opinau/cv/Modul1/Docs/IMG_20200708_190415.jpg

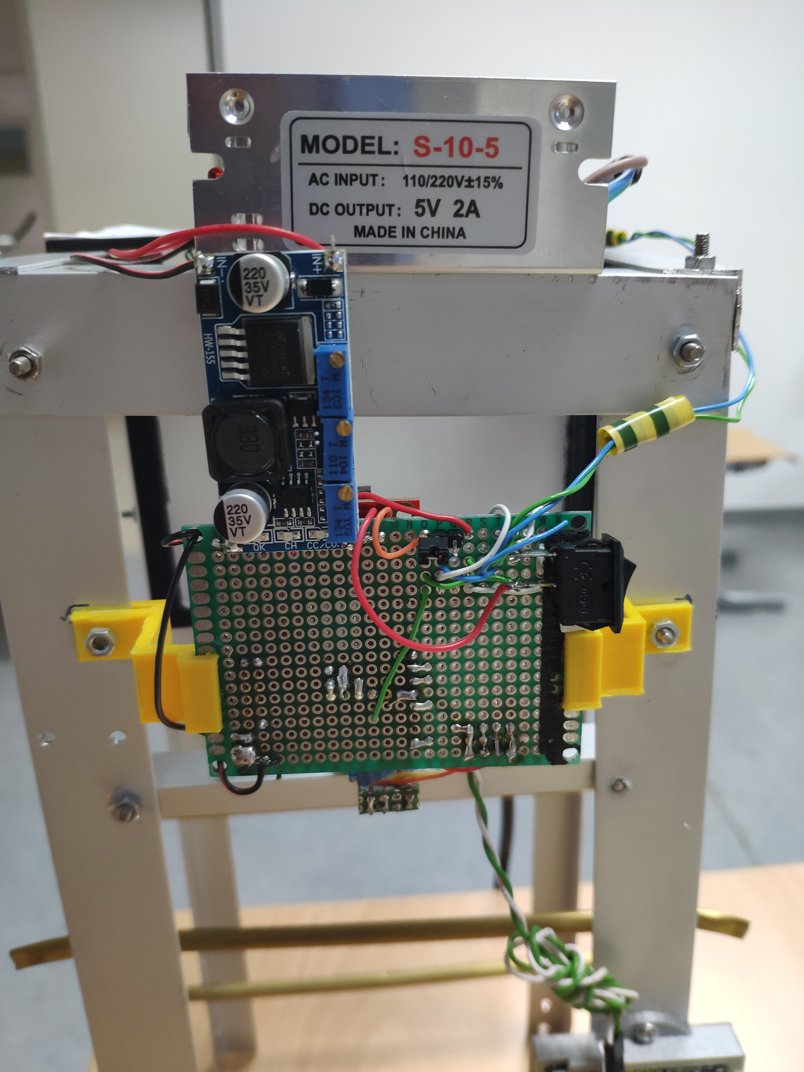
Modul1/Docs/IMG_20200708_190415.jpg
