opinau/cv/Modul1/Docs/IMG_20200708_190424.jpg

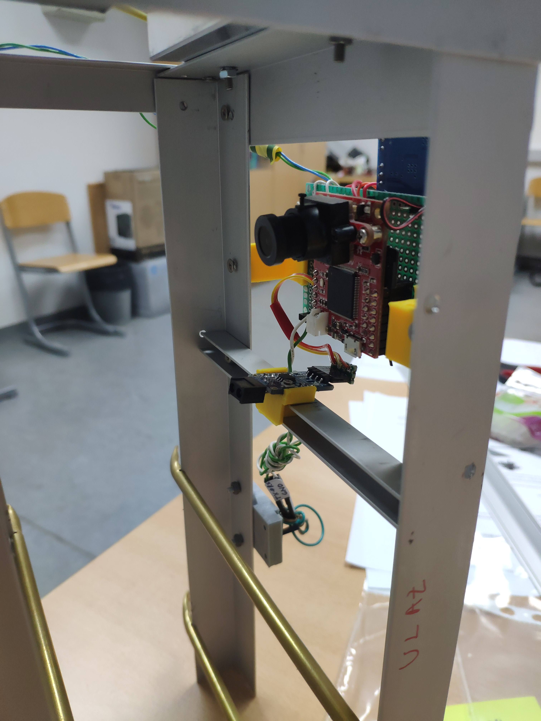
Modul1/Docs/IMG_20200708_190424.jpg
