opinau/cv/Modul1/Docs/visualisation_1.jpg

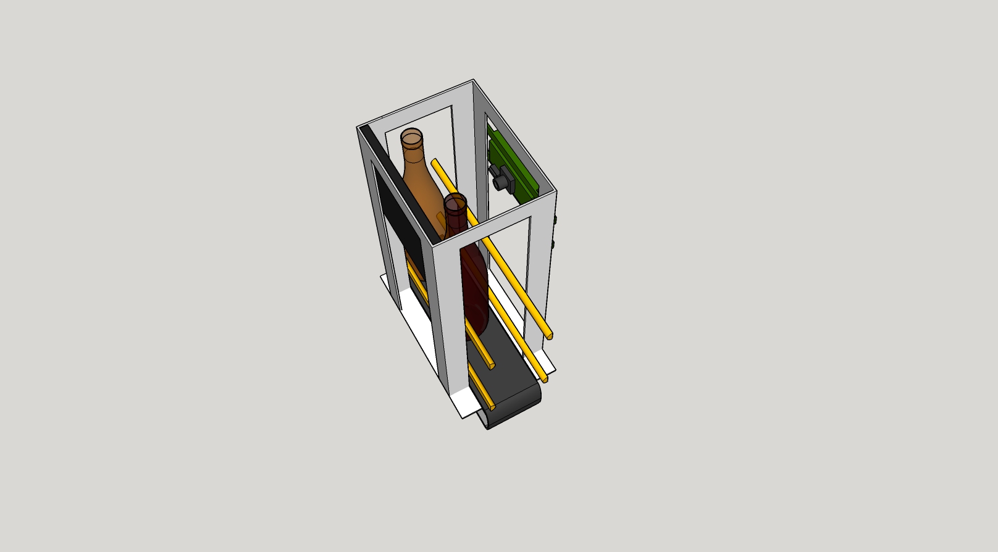
Modul1/Docs/visualisation_1.jpg
