opinau/cv/Modul1/Docs/visualisation_2.jpg

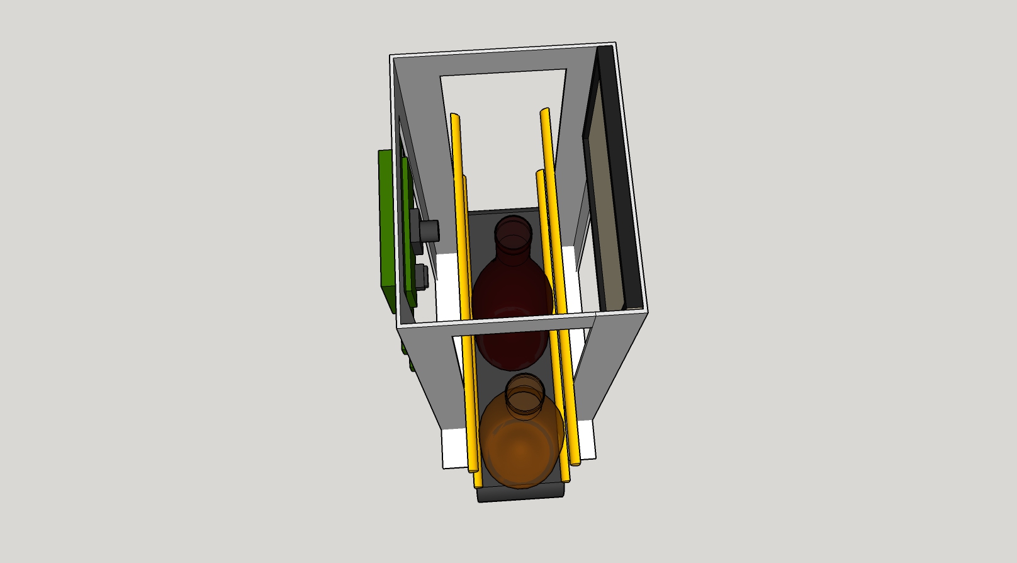
Modul1/Docs/visualisation_2.jpg
