opinau/cv/Modul1/Docs/visualisation_3.jpg

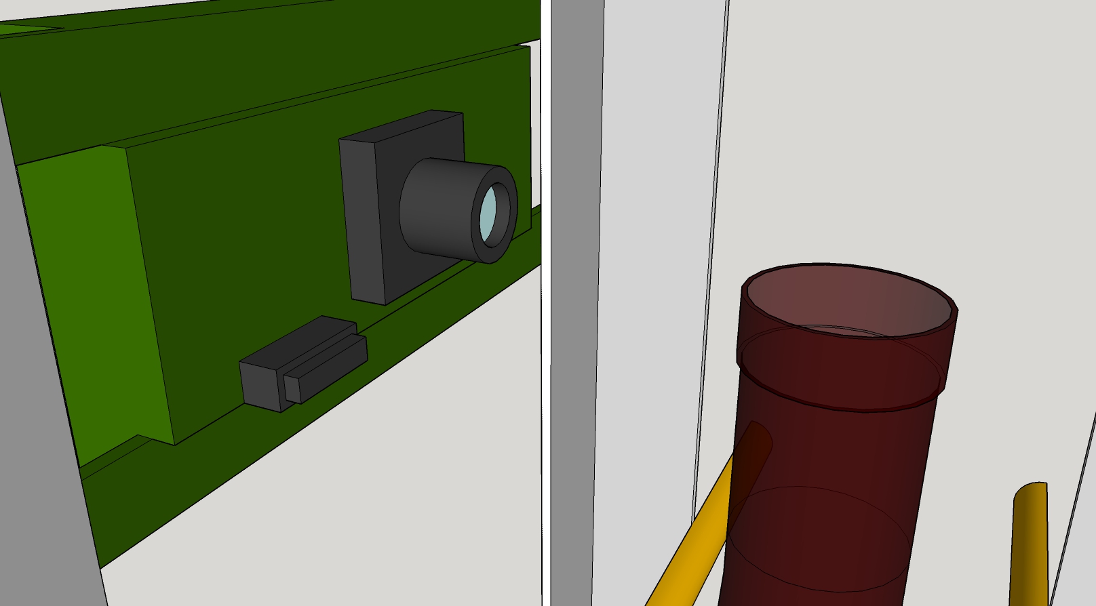
Modul1/Docs/visualisation_3.jpg
