opinau/cv/Modul1/Docs/visualisation_4.jpg

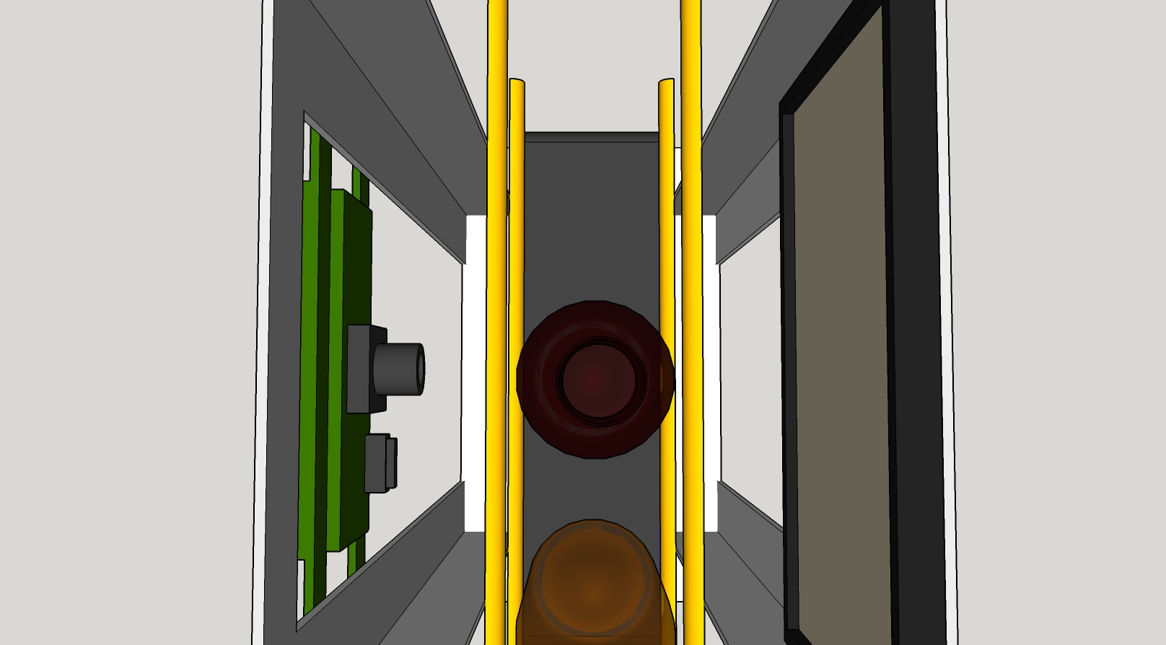
Modul1/Docs/visualisation_4.jpg
