opinau/cv/Modul2/Docs/IMG_20200710_142603.jpg

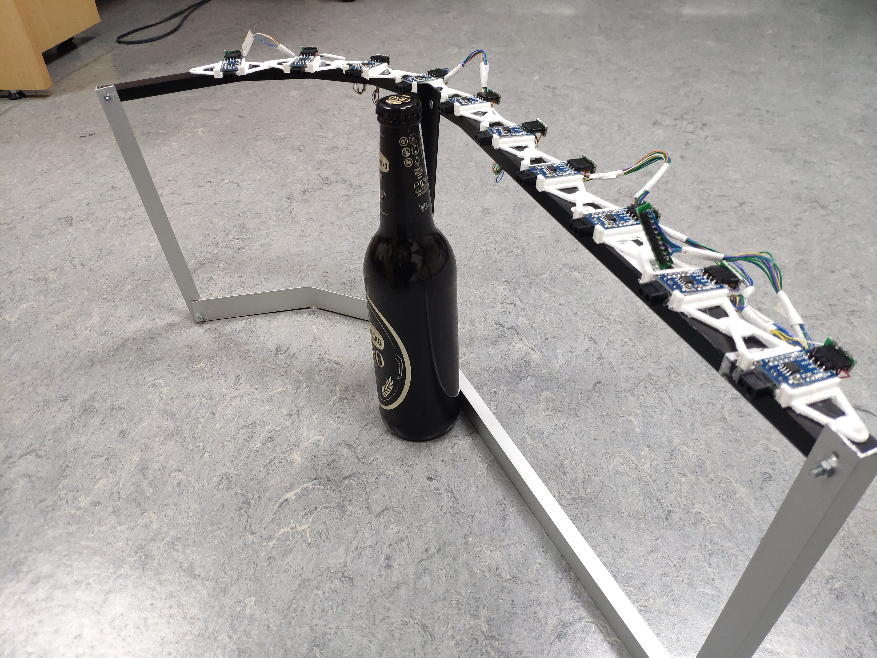
Modul2/Docs/IMG_20200710_142603.jpg
