opinau/cv/Modul2/Docs/IMG_20200710_144241.jpg

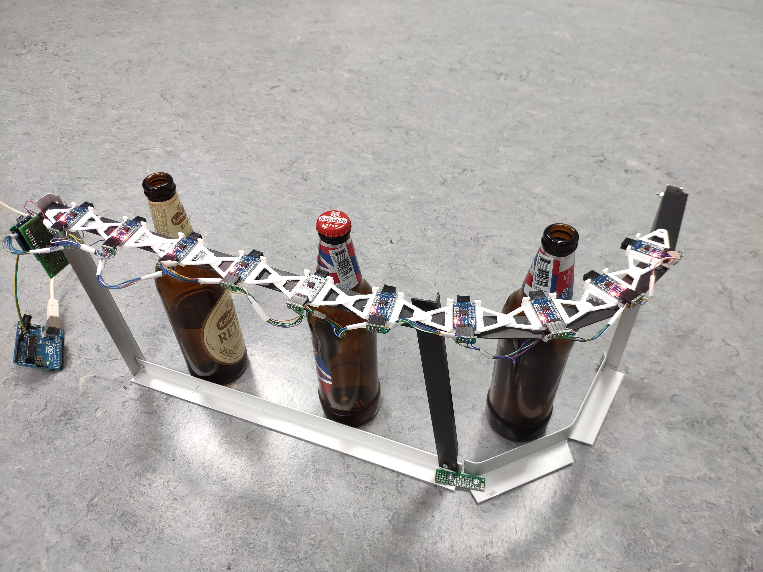
Modul2/Docs/IMG_20200710_144241.jpg
