opinau/cv/Modul2/Docs/IMG_20200710_144505.jpg

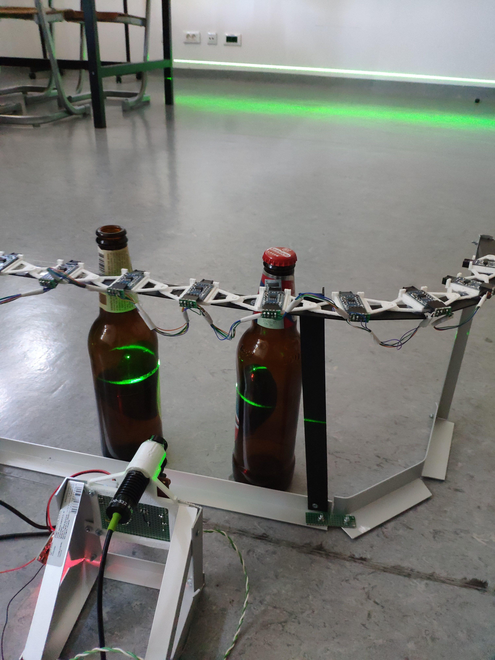
Modul2/Docs/IMG_20200710_144505.jpg
