opinau/cv/Modul2/Docs/slikaCep7_v2.png

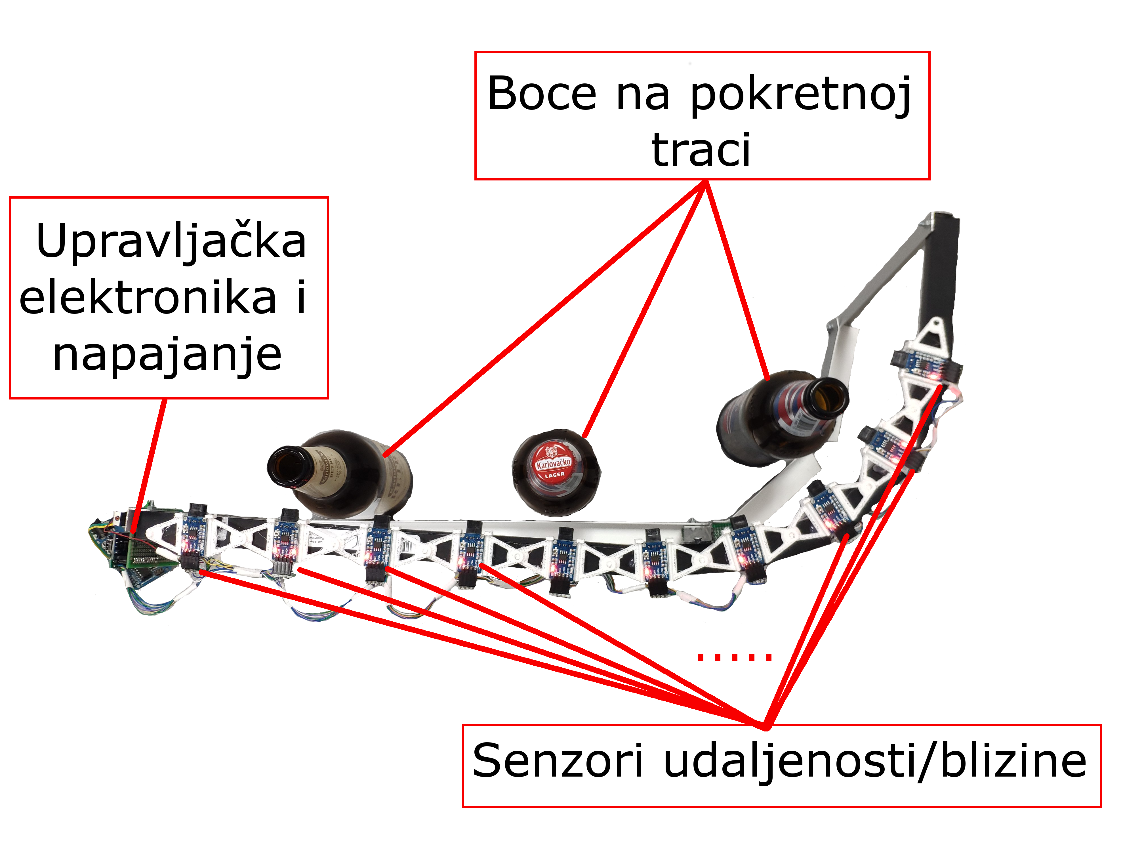
Modul2/Docs/slikaCep7_v2.png
