opinau/cv/Modul2/Docs/slikaCep9.png

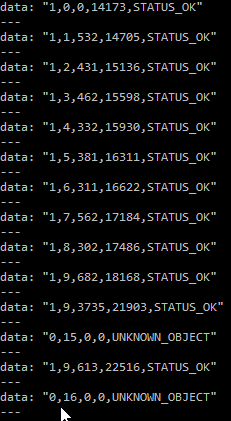
Modul2/Docs/slikaCep9.png
