opinau/cv/Modul2/Docs/visualisation1.jpg

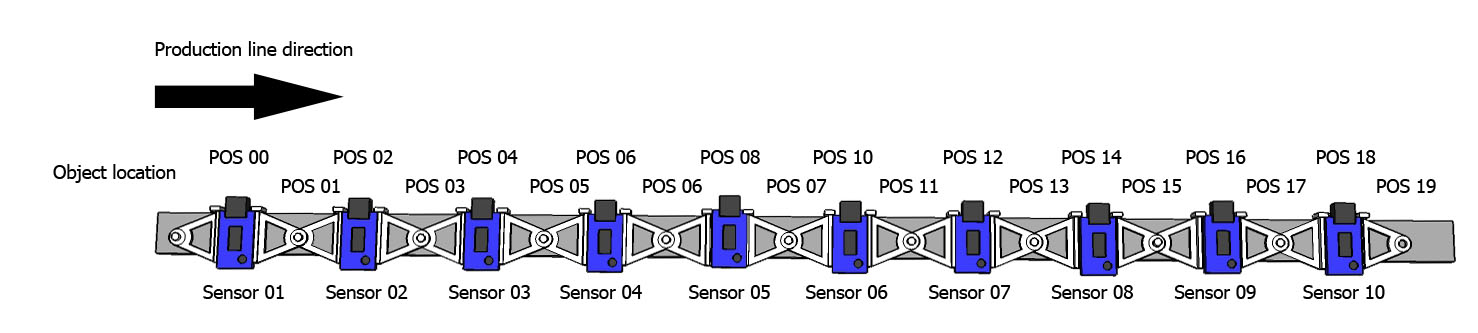
Modul2/Docs/visualisation1.jpg
