opinau/cv/Modul2/Docs/visualisation2.jpg

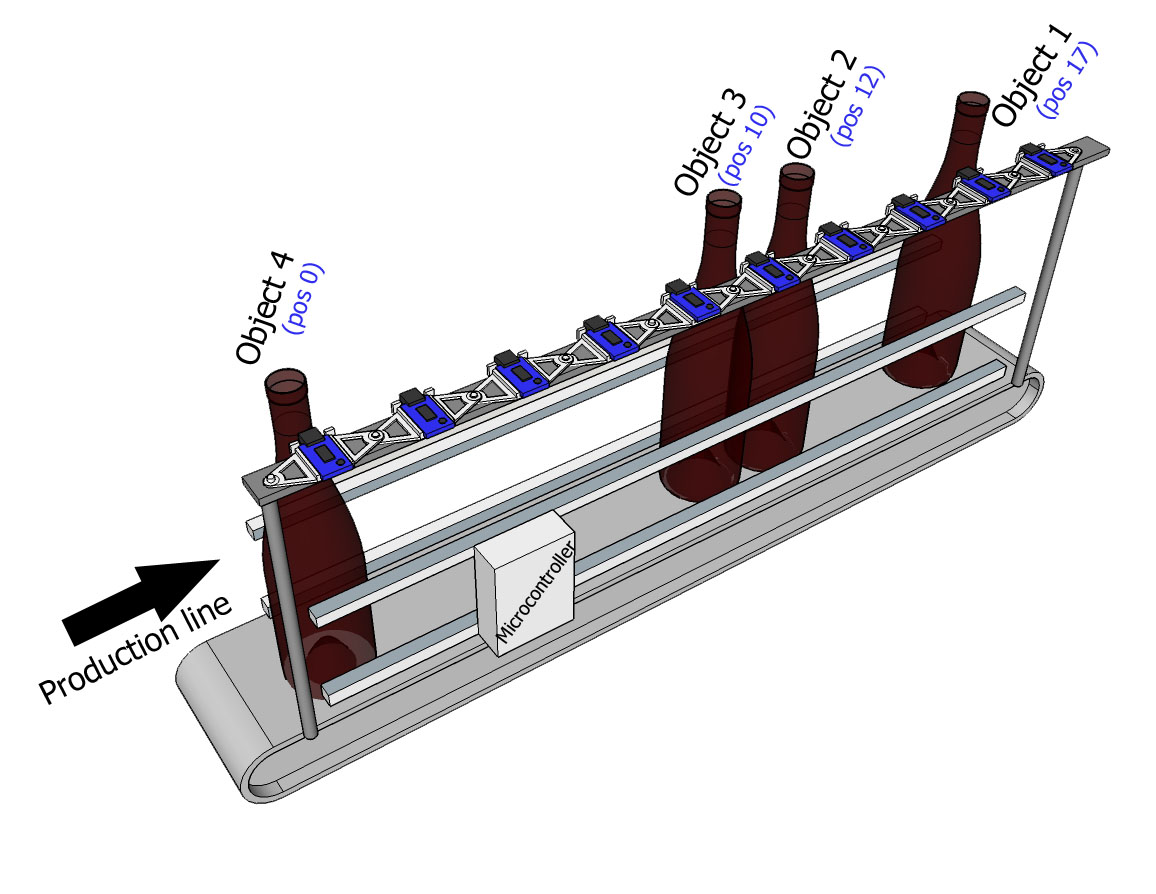
Modul2/Docs/visualisation2.jpg
