opinau/cv/Modul3/Docs/IMG_20200708_190440.jpg

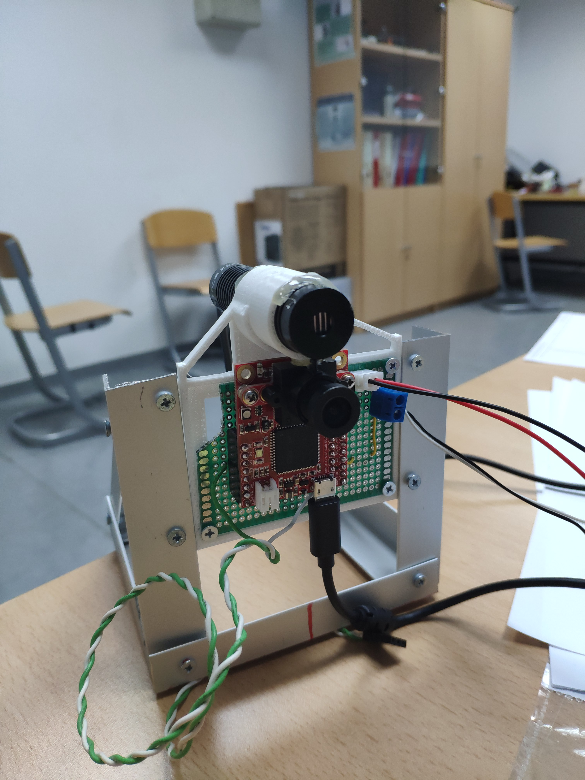
Modul3/Docs/IMG_20200708_190440.jpg
