opinau/cv/Modul3/Docs/IMG_20200708_190444.jpg

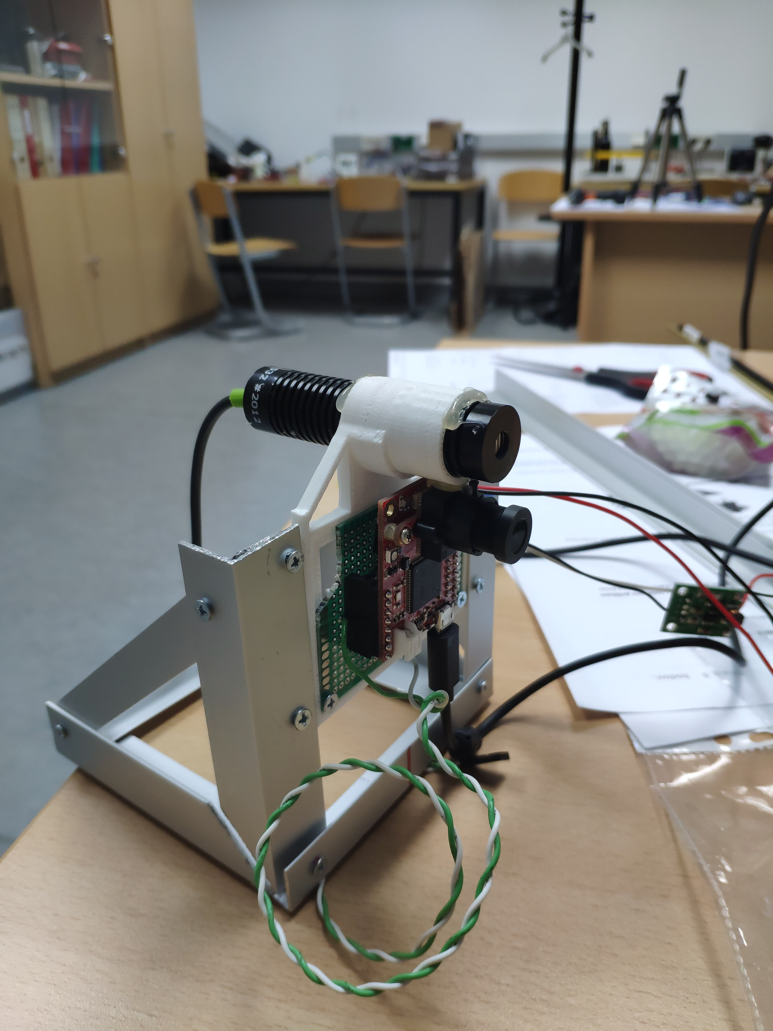
Modul3/Docs/IMG_20200708_190444.jpg
