opinau/cv/Modul3/Docs/matlab_fig_distanceat300mm.jpg

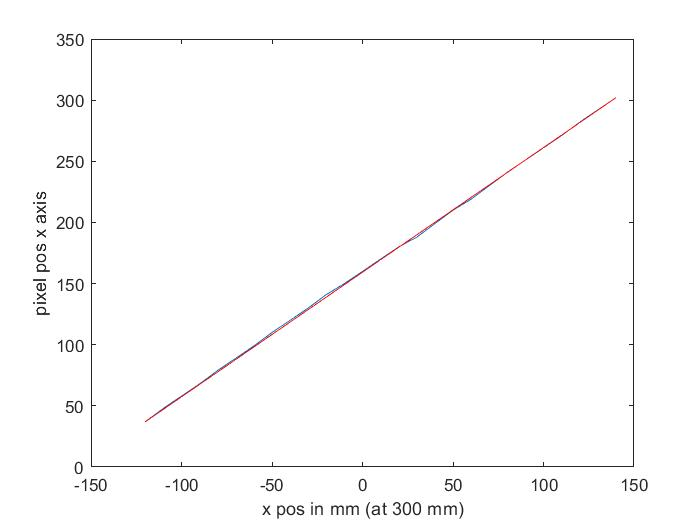
Modul3/Docs/matlab_fig_distanceat300mm.jpg
