opinau/cv/Modul3/Docs/visualisation1.jpg

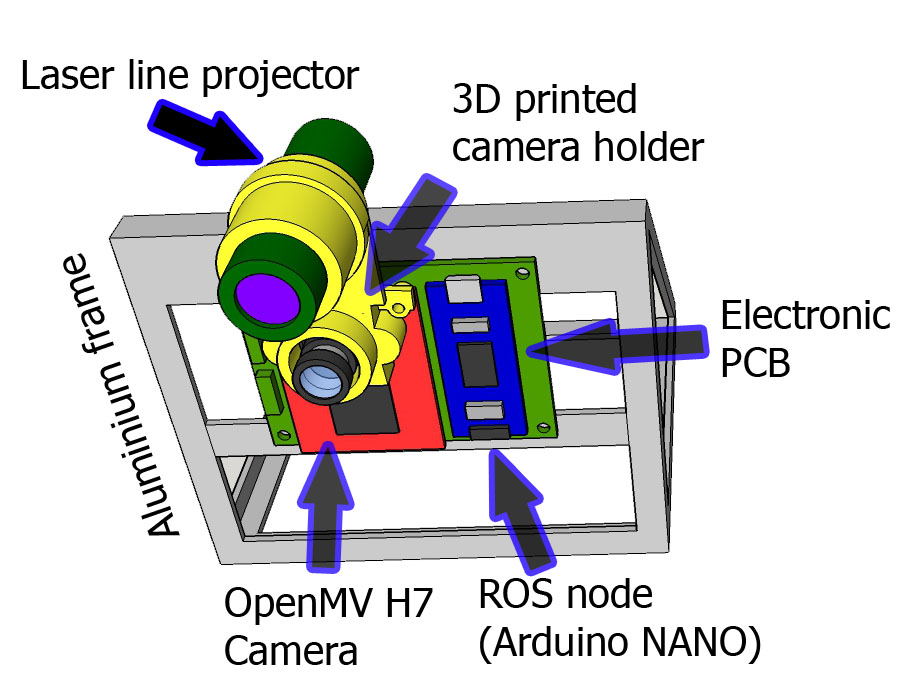
Modul3/Docs/visualisation1.jpg
